entropia/vaporlight/vaporware/led-boards/stm_include/stm32/spi.h

/*
 * This file is part of the libopencm3 project.
 *
 * Copyright (C) 2009 Uwe Hermann <uwe@hermann-uwe.de>
 *
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
 * You should have received a copy of the GNU Lesser General Public License
 * along with this program.  If not, see <http://www.gnu.org/licenses/>.
 */

#ifndef LIBOPENCM3_SPI_H
#define LIBOPENCM3_SPI_H

#include "memorymap.h"
#include "../cm3/common.h"

/* Registers can be accessed as 16bit or 32bit values. */

/* --- Convenience macros -------------------------------------------------- */

#define SPI1				SPI1_BASE
#define SPI2				SPI2_I2S_BASE
#define SPI3				SPI3_I2S_BASE

/* --- SPI registers ------------------------------------------------------- */

/* Control register 1 (SPIx_CR1) */
#define SPI_CR1(spi_base)		MMIO32(spi_base + 0x00)
#define SPI1_CR1			SPI_CR1(SPI1_BASE)
#define SPI2_CR1			SPI_CR1(SPI2_I2S_BASE)
#define SPI3_CR1			SPI_CR1(SPI3_I2S_BASE)

/* Control register 2 (SPIx_CR2) */
#define SPI_CR2(spi_base)		MMIO32(spi_base + 0x04)
#define SPI1_CR2			SPI_CR2(SPI1_BASE)
#define SPI2_CR2			SPI_CR2(SPI2_I2S_BASE)
#define SPI3_CR2			SPI_CR2(SPI3_I2S_BASE)

/* Status register (SPIx_SR) */
#define SPI_SR(spi_base)		MMIO32(spi_base + 0x08)
#define SPI1_SR				SPI_SR(SPI1_BASE)
#define SPI2_SR				SPI_SR(SPI2_I2S_BASE)
#define SPI3_SR				SPI_SR(SPI3_I2S_BASE)

/* Data register (SPIx_DR) */
#define SPI_DR(spi_base)		MMIO32(spi_base + 0x0c)
#define SPI1_DR				SPI_DR(SPI1_BASE)
#define SPI2_DR				SPI_DR(SPI2_I2S_BASE)
#define SPI3_DR				SPI_DR(SPI3_I2S_BASE)

/* CRC polynomial register (SPIx_CRCPR) */
/* Note: Not used in I2S mode. */
#define SPI_CRCPR(spi_base)		MMIO32(spi_base + 0x10)
#define SPI1_CRCPR			SPI_CRCPR(SPI1_BASE)
#define SPI2_CRCPR			SPI_CRCPR(SPI2_I2S_BASE)
#define SPI3_CRCPR			SPI_CRCPR(SPI3_I2S_BASE)

/* RX CRC register (SPIx_RXCRCR) */
/* Note: Not used in I2S mode. */
#define SPI_RXCRCR(spi_base)		MMIO32(spi_base + 0x14)
#define SPI1_RXCRCR			SPI_RXCRCR(SPI1_BASE)
#define SPI2_RXCRCR			SPI_RXCRCR(SPI2_I2S_BASE)
#define SPI3_RXCRCR			SPI_RXCRCR(SPI3_I2S_BASE)

/* TX CRC register (SPIx_RXCRCR) */
/* Note: Not used in I2S mode. */
#define SPI_TXCRCR(spi_base)		MMIO32(spi_base + 0x18)
#define SPI1_TXCRCR			SPI_TXCRCR(SPI1_BASE)
#define SPI2_TXCRCR			SPI_TXCRCR(SPI2_I2S_BASE)
#define SPI3_TXCRCR			SPI_TXCRCR(SPI3_I2S_BASE)

/* I2S configuration register (SPIx_I2SCFGR) */
#define SPI_I2SCFGR(spi_base)		MMIO32(spi_base + 0x1c)
#define SPI1_I2SCFGR			SPI_I2SCFGR(SPI1_BASE)
#define SPI2_I2SCFGR			SPI_I2SCFGR(SPI2_I2S_BASE)
#define SPI3_I2SCFGR			SPI_I2SCFGR(SPI3_I2S_BASE)

/* I2S prescaler register (SPIx_I2SPR) */
#define SPI_I2SPR(spi_base)		MMIO32(spi_base + 0x20)
#define SPI1_I2SPR			SPI_I2SPR(SPI1_BASE)
#define SPI2_I2SPR			SPI_I2SPR(SPI2_I2S_BASE)
#define SPI3_I2SPR			SPI_I2SPR(SPI3_I2S_BASE)

/* --- SPI_CR1 values ------------------------------------------------------ */

/* Note: None of the CR1 bits are used in I2S mode. */

/* BIDIMODE: Bidirectional data mode enable */
#define SPI_CR1_BIDIMODE_2LINE_UNIDIR	(0 << 15)
#define SPI_CR1_BIDIMODE_1LINE_BIDIR	(1 << 15)
#define SPI_CR1_BIDIMODE		(1 << 15)

/* BIDIOE: Output enable in bidirectional mode */
#define SPI_CR1_BIDIOE			(1 << 14)

/* CRCEN: Hardware CRC calculation enable */
#define SPI_CR1_CRCEN			(1 << 13)

/* CRCNEXT: Transmit CRC next */
#define SPI_CR1_CRCNEXT			(1 << 12)

/* DFF: Data frame format */
#define SPI_CR1_DFF_8BIT		(0 << 11)
#define SPI_CR1_DFF_16BIT		(1 << 11)
#define SPI_CR1_DFF			(1 << 11)

/* RXONLY: Receive only */
#define SPI_CR1_RXONLY			(1 << 10)

/* SSM: Software slave management */
#define SPI_CR1_SSM			(1 << 9)

/* SSI: Internal slave select */
#define SPI_CR1_SSI			(1 << 8)

/* LSBFIRST: Frame format */
#define SPI_CR1_MSBFIRST		(0 << 7)
#define SPI_CR1_LSBFIRST		(1 << 7)

/* SPE: SPI enable */
#define SPI_CR1_SPE			(1 << 6)

/* BR[2:0]: Baud rate control */
#define SPI_CR1_BAUDRATE_FPCLK_DIV_2	(0x00 << 3)
#define SPI_CR1_BAUDRATE_FPCLK_DIV_4	(0x01 << 3)
#define SPI_CR1_BAUDRATE_FPCLK_DIV_8	(0x02 << 3)
#define SPI_CR1_BAUDRATE_FPCLK_DIV_16	(0x03 << 3)
#define SPI_CR1_BAUDRATE_FPCLK_DIV_32	(0x04 << 3)
#define SPI_CR1_BAUDRATE_FPCLK_DIV_64	(0x05 << 3)
#define SPI_CR1_BAUDRATE_FPCLK_DIV_128	(0x06 << 3)
#define SPI_CR1_BAUDRATE_FPCLK_DIV_256	(0x07 << 3)
#define SPI_CR1_BR_FPCLK_DIV_2		0x0
#define SPI_CR1_BR_FPCLK_DIV_4		0x1
#define SPI_CR1_BR_FPCLK_DIV_8		0x2
#define SPI_CR1_BR_FPCLK_DIV_16		0x3
#define SPI_CR1_BR_FPCLK_DIV_32		0x4
#define SPI_CR1_BR_FPCLK_DIV_64		0x5
#define SPI_CR1_BR_FPCLK_DIV_128	0x6
#define SPI_CR1_BR_FPCLK_DIV_256	0x7

/* MSTR: Master selection */
#define SPI_CR1_MSTR			(1 << 2)

/* CPOL: Clock polarity */
#define SPI_CR1_CPOL_CLK_TO_0_WHEN_IDLE	(0 << 1)
#define SPI_CR1_CPOL_CLK_TO_1_WHEN_IDLE	(1 << 1)
#define SPI_CR1_CPOL			(1 << 1)

/* CPHA: Clock phase */
#define SPI_CR1_CPHA_CLK_TRANSITION_1	(0 << 0)
#define SPI_CR1_CPHA_CLK_TRANSITION_2	(1 << 0)
#define SPI_CR1_CPHA			(1 << 0)

/* --- SPI_CR1 values ------------------------------------------------------ */

/* Bits [15:8]: Reserved. Forced to 0 by hardware. */

/* TXEIE: Tx buffer empty interrupt enable */
#define SPI_CR2_TXEIE			(1 << 7)

/* RXNEIE: RX buffer not empty interrupt enable */
#define SPI_CR2_RXNEIE			(1 << 6)

/* ERRIE: Error interrupt enable */
#define SPI_CR2_ERRIE			(1 << 5)

/* Bits [4:3]: Reserved. Forced to 0 by hardware. */

/* SSOE: SS output enable */
#define SPI_CR2_SSOE			(1 << 2)

/* TXDMAEN: Tx buffer DMA enable */
#define SPI_CR2_TXDMAEN			(1 << 1)

/* RXDMAEN: Rx buffer DMA enable */
#define SPI_CR2_RXDMAEN			(1 << 0)

/* --- SPI_SR values ------------------------------------------------------- */

/* Bits [15:8]: Reserved. Forced to 0 by hardware. */

/* BSY: Busy flag */
#define SPI_SR_BSY			(1 << 7)

/* OVR: Overrun flag */
#define SPI_SR_OVR			(1 << 6)

/* MODF: Mode fault */
#define SPI_SR_MODF			(1 << 5)

/* CRCERR: CRC error flag */
#define SPI_SR_CRCERR			(1 << 4)

/* UDR: Underrun flag */
#define SPI_SR_UDR			(1 << 3)

/* CHSIDE: Channel side */
#define SPI_SR_CHSIDE			(1 << 2)

/* TXE: Transmit buffer empty */
#define SPI_SR_TXE			(1 << 1)

/* RXNE: Receive buffer not empty */
#define SPI_SR_RXNE			(1 << 0)

/* --- SPI_SR values ------------------------------------------------------- */

/* SPI_DR[15:0]: Data Register. */

/* --- SPI_CRCPR values ---------------------------------------------------- */

/* SPI_CRCPR [15:0]: CRC Polynomial Register. */

/* --- SPI_RXCRCR values --------------------------------------------------- */

/* SPI_RXCRCR [15:0]: RX CRC Register. */

/* --- SPI_TXCRCR values --------------------------------------------------- */

/* SPI_TXCRCR [15:0]: TX CRC Register. */

/* --- SPI_I2SCFGR values -------------------------------------------------- */

/* Bits [15:12]: Reserved. Forced to 0 by hardware. */

/* I2SMOD: I2S mode selection */
#define SPI_I2SCFGR_I2SMOD			(1 << 11)

/* I2SE: I2S Enable */
#define SPI_I2SCFGR_I2SE			(1 << 10)

/* I2SCFG[9:8]: I2S configuration mode */
#define SPI_I2SCFGR_I2SCFG_LSB			8
#define SPI_I2SCFGR_I2SCFG_SLAVE_TRANSMIT	0x0
#define SPI_I2SCFGR_I2SCFG_SLAVE_RECEIVE	0x1
#define SPI_I2SCFGR_I2SCFG_MASTER_TRANSMIT	0x2
#define SPI_I2SCFGR_I2SCFG_MASTER_RECEIVE	0x3

/* PCMSYNC: PCM frame synchronization */
#define SPI_I2SCFGR_PCMSYNC			(1 << 7)

/* Bit 6: Reserved. Forced to 0 by hardware. */

/* I2SSTD[5:4]: I2S standard selection */
#define SPI_I2SCFGR_I2SSTD_LSB			4
#define SPI_I2SCFGR_I2SSTD_I2S_PHILLIPS		0x0
#define SPI_I2SCFGR_I2SSTD_MSB_JUSTIFIED	0x1
#define SPI_I2SCFGR_I2SSTD_LSB_JUSTIFIED	0x2
#define SPI_I2SCFGR_I2SSTD_PCM			0x3

/* CKPOL: Steady state clock polarity */
#define SPI_I2SCFGR_CKPOL			(1 << 3)

/* DATLEN[2:1]: Data length to be transferred */
#define SPI_I2SCFGR_DATLEN_LSB			1
#define SPI_I2SCFGR_DATLEN_16BIT		0x0
#define SPI_I2SCFGR_DATLEN_24BIT		0x1
#define SPI_I2SCFGR_DATLEN_32BIT		0x2

/* CHLEN: Channel length */
#define SPI_I2SCFGR_CHLEN			(1 << 0)

/* --- SPI_I2SPR values ---------------------------------------------------- */

/* Bits [15:10]: Reserved. Forced to 0 by hardware. */

/* MCKOE: Master clock output enable */
#define SPI_I2SPR_MCKOE				(1 << 9)

/* ODD: Odd factor for the prescaler */
#define SPI_I2SPR_ODD				(1 << 8)

/* I2SDIV[7:0]: I2S Linear prescaler */
/* 0 and 1 are forbidden values */

#endif
