entropia/vaporlight/vaporware/led-boards/stm_include/stm32/scb.h

/*
 * This file is part of the libopencm3 project.
 *
 * Copyright (C) 2010 Piotr Esden-Tempski <piotr@esden.net>
 * Copyright (C) 2010 Thomas Otto <tommi@viadmin.org>
 *
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
 * You should have received a copy of the GNU Lesser General Public License
 * along with this program.  If not, see <http://www.gnu.org/licenses/>.
 */

#ifndef LIBOPENCM3_SCB_H
#define LIBOPENCM3_SCB_H

#include "memorymap.h"
#include "../cm3/common.h"

/* --- SCB: Registers ------------------------------------------------------ */

/* CPUID: CPUID base register */
#define SCB_CPUID                       MMIO32(SCB_BASE + 0x00)

/* ICSR: Interrupt Control State Register */
#define SCB_ICSR                        MMIO32(SCB_BASE + 0x04)

/* VTOR: Vector Table Offset Register */
#define SCB_VTOR                        MMIO32(SCB_BASE + 0x08)

/* AIRCR: Application Interrupt and Reset Control Register */
#define SCB_AIRCR                       MMIO32(SCB_BASE + 0x0C)

/* SCR: System Control Register */
#define SCB_SCR                         MMIO32(SCB_BASE + 0x10)

/* CCR: Configuration Control Register */
#define SCB_CCR                         MMIO32(SCB_BASE + 0x14)

/* SHP: System Handler Priority Registers */
/* Note: 12 8bit registers */
#define SCB_SHPR(shpr_id)               MMIO8(SCB_BASE + 0x18 + shpr_id)
#define SCB_SHPR1			MMIO8(SCB_BASE + 0x18 + 1)
#define SCB_SHPR2			MMIO8(SCB_BASE + 0x18 + 2)
#define SCB_SHPR3			MMIO8(SCB_BASE + 0x18 + 3)

/* SHCSR: System Handler Control and State Register */
#define SCB_SHCSR                       MMIO32(SCB_BASE + 0x24)

/* CFSR: Configurable Fault Status Registers */
#define SCB_CFSR                        MMIO32(SCB_BASE + 0x28)

/* HFSR: Hard Fault Status Register */
#define SCB_HFSR                        MMIO32(SCB_BASE + 0x2C)

/* DFSR: Debug Fault Status Register */
#define SCB_DFSR                        MMIO32(SCB_BASE + 0x30)

/* MMFAR: Memory Manage Fault Address Register */
#define SCB_MMFAR                       MMIO32(SCB_BASE + 0x34)

/* BFAR: Bus Fault Address Register */
#define SCB_BFAR                        MMIO32(SCB_BASE + 0x38)

/* AFSR: Auxiliary Fault Status Register */
#define SCB_AFSR                        MMIO32(SCB_BASE + 0x3C)

/* --- SCB values ---------------------------------------------------------- */

/* --- SCB_CPUID values ---------------------------------------------------- */

/* Implementer[31:24]: Implementer code */
#define SCP_CPUID_IMPLEMENTER_LSB		24
/* Variant[23:20]: Variant number */
#define SCP_CPUID_VARIANT_LSB			20
/* Constant[19:16]: Reads as 0xF */
#define SCP_CPUID_CONSTANT_LSB			16
/* PartNo[15:4]: Part number of the processor */
#define SCP_CPUID_PARTNO_LSB			4
/* Revision[3:0]: Revision number */
#define SCP_CPUID_REVISION_LSB			0

/* --- SCB_ICSR values ----------------------------------------------------- */

/* NMIPENDSET: NMI set-pending bit */
#define SCB_ICSR_NMIPENDSET			(1 << 31)
/* Bits [30:29]: reserved - must be kept cleared */
/* PENDSVSET: PendSV set-pending bit */
#define SCB_ICSR_PENDSVSET			(1 << 28)
/* PENDSVCLR: PendSV clear-pending bit */
#define SCB_ICSR_PENDSVCLR			(1 << 27)
/* PENDSTSET: SysTick exception set-pending bit */
#define SCB_ICSR_PENDSTSET			(1 << 26)
/* PENDSTCLR: SysTick exception clear-pending bit */
#define SCB_ICSR_PENDSTCLR			(1 << 25)
/* Bit 24: reserved - must be kept cleared */
/* Bit 23: reserved for debug - reads as 0 when not in debug mode */
/* ISRPENDING: Interrupt pending flag, excluding NMI and Faults */
#define SCB_ICSR_ISRPENDING			(1 << 22)
/* VECTPENDING[21:12] Pending vector */
#define SCB_ICSR_VECTPENDING_LSB		12
/* RETOBASE: Return to base level */
#define SCB_ICSR_RETOBASE			(1 << 11)
/* Bits [10:9]: reserved - must be kept cleared */
/* VECTACTIVE[8:0] Active vector */
#define SCB_ICSR_VECTACTIVE_LSB			0

/* --- SCB_VTOR values ----------------------------------------------------- */

/* Bits [31:30]: reserved - must be kept cleared */
/* TBLOFF[29:9]: Vector table base offset field */
#define SCB_VTOR_TBLOFF_LSB			9	/* inconsistent datasheet - LSB could be 11 */

/* --- SCB_AIRCR values ---------------------------------------------------- */

/* VECTKEYSTAT[31:16]/ VECTKEY[31:16] Register key */
#define SCB_AIRCR_VECTKEYSTAT_LSB		16
#define SCB_AIRCR_VECTKEY			0x05FA0000
/* ENDIANESS Data endianness bit */
#define SCB_AIRCR_ENDIANESS			(1 << 15)
/* Bits [14:11]: reserved - must be kept cleared */
/* PRIGROUP[10:8]: Interrupt priority grouping field */
#define SCB_AIRCR_PRIGROUP_LSB			8
#define SCB_AIRCR_PRIGROUP_GROUP16_NOSUB	0x3
#define SCB_AIRCR_PRIGROUP_GROUP8_SUB2		0x4
#define SCB_AIRCR_PRIGROUP_GROUP4_SUB4		0x5
#define SCB_AIRCR_PRIGROUP_GROUP2_SUB8		0x6
#define SCB_AIRCR_PRIGROUP_NOGROUP_SUB16	0x7
/* Bits [7:3]: reserved - must be kept cleared */
/* SYSRESETREQ System reset request */
#define SCB_AIRCR_SYSRESETREQ			(1 << 2)
/* VECTCLRACTIVE */
#define SCB_AIRCR_VECTCLRACTIVE			(1 << 1)
/* VECTRESET */
#define SCB_AIRCR_VECTRESET			(1 << 0)

/* --- SCB_SCR values ------------------------------------------------------ */

/* Bits [31:5]: reserved - must be kept cleared */
/* SEVEONPEND Send Event on Pending bit */
#define SCB_SCR_SEVEONPEND			(1 << 4)
/* Bit 3: reserved - must be kept cleared */
/* SLEEPDEEP */
#define SCB_SCR_SLEEPDEEP			(1 << 2)
/* SLEEPONEXIT */
#define SCB_SCR_SLEEPONEXIT			(1 << 1)
/* Bit 0: reserved - must be kept cleared */

/* --- SCB_CCR values ------------------------------------------------------ */

/* Bits [31:10]: reserved - must be kept cleared */
/* STKALIGN */
#define SCB_CCR_STKALIGN			(1 << 9)
/* BFHFNMIGN */
#define SCB_CCR_BFHFNMIGN			(1 << 8)
/* Bits [7:5]: reserved - must be kept cleared */
/* DIV_0_TRP */
#define SCB_CCR_DIV_0_TRP			(1 << 4)
/* UNALIGN_TRP */
#define SCB_CCR_UNALIGN_TRP			(1 << 3)
/* Bit 2: reserved - must be kept cleared */
/* USERSETMPEND */
#define SCB_CCR_USERSETMPEND			(1 << 1)
/* NONBASETHRDENA */
#define SCB_CCR_NONBASETHRDENA			(1 << 0)

/* --- SCB_SHPR1 values ---------------------------------------------------- */

/* Bits [31:24]: reserved - must be kept cleared */
/* PRI_6[23:16]: Priority of system handler 6, usage fault */
#define SCB_SHPR1_PRI_6_LSB			16
/* PRI_5[15:8]: Priority of system handler 5, bus fault */
#define SCB_SHPR1_PRI_5_LSB			8
/* PRI_4[7:0]: Priority of system handler 4, memory management fault */
#define SCB_SHPR1_PRI_4_LSB			0

/* --- SCB_SHPR2 values ---------------------------------------------------- */

/* PRI_11[31:24]: Priority of system handler 11, SVCall */
#define SCB_SHPR2_PRI_11_LSB			24
/* Bits [23:0]: reserved - must be kept cleared */

/* --- SCB_SHPR3 values ---------------------------------------------------- */

/* PRI_15[31:24]: Priority of system handler 15, SysTick exception */
#define SCB_SHPR3_PRI_15_LSB			24
/* PRI_14[23:16]: Priority of system handler 14, PendSV */
#define SCB_SHPR3_PRI_14_LSB			16
/* Bits [15:0]: reserved - must be kept cleared */

/* --- SCB_SHCSR values ---------------------------------------------------- */

/* Bits [31:19]: reserved - must be kept cleared */
/* USGFAULTENA: Usage fault enable */
#define SCB_SHCSR_USGFAULTENA			(1 << 18)
/* BUSFAULTENA: Bus fault enable */
#define SCB_SHCSR_BUSFAULTENA			(1 << 17)
/* MEMFAULTENA: Memory management fault enable */
#define SCB_SHCSR_MEMFAULTENA			(1 << 16)
/* SVCALLPENDED: SVC call pending */
#define SCB_SHCSR_SVCALLPENDED			(1 << 15)
/* BUSFAULTPENDED: Bus fault exception pending */
#define SCB_SHCSR_BUSFAULTPENDED		(1 << 14)
/* MEMFAULTPENDED: Memory management fault exception pending */
#define SCB_SHCSR_MEMFAULTPENDED		(1 << 13)
/* USGFAULTPENDED: Usage fault exception pending */
#define SCB_SHCSR_USGFAULTPENDED		(1 << 12)
/* SYSTICKACT: SysTick exception active */
#define SCB_SHCSR_SYSTICKACT			(1 << 11)
/* PENDSVACT: PendSV exception active */
#define SCB_SHCSR_PENDSVACT			(1 << 10)
/* Bit 9: reserved - must be kept cleared */
/* MONITORACT: Debug monitor active */
#define SCB_SHCSR_MONITORACT			(1 << 8)
/* SVCALLACT: SVC call active */
#define SCB_SHCSR_SVCALLACT			(1 << 7)
/* Bits [6:4]: reserved - must be kept cleared */
/* USGFAULTACT: Usage fault exception active */
#define SCB_SHCSR_USGFAULTACT			(1 << 3)
/* Bit 2: reserved - must be kept cleared */
/* BUSFAULTACT: Bus fault exception active */
#define SCB_SHCSR_BUSFAULTACT			(1 << 1)
/* MEMFAULTACT: Memory management fault exception active */
#define SCB_SHCSR_MEMFAULTACT			(1 << 0)

/* --- SCB_CFSR values ----------------------------------------------------- */

/* Bits [31:26]: reserved - must be kept cleared */
/* DIVBYZERO: Divide by zero usage fault */
#define SCB_CFSR_DIVBYZERO			(1 << 25)
/* UNALIGNED: Unaligned access usage fault */
#define SCB_CFSR_UNALIGNED			(1 << 24)
/* Bits [23:20]: reserved - must be kept cleared */
/* NOCP: No coprocessor usage fault */
#define SCB_CFSR_NOCP				(1 << 19)
/* INVPC: Invalid PC load usage fault */
#define SCB_CFSR_INVPC				(1 << 18)
/* INVSTATE: Invalid state usage fault */
#define SCB_CFSR_INVSTATE			(1 << 17)
/* UNDEFINSTR: Undefined instruction usage fault */
#define SCB_CFSR_UNDEFINSTR			(1 << 16)
/* BFARVALID: Bus Fault Address Register (BFAR) valid flag */
#define SCB_CFSR_BFARVALID			(1 << 15)
/* Bits [14:13]: reserved - must be kept cleared */
/* STKERR: Bus fault on stacking for exception entry */
#define SCB_CFSR_STKERR				(1 << 12)
/* UNSTKERR: Bus fault on unstacking for a return from exception */
#define SCB_CFSR_UNSTKERR			(1 << 11)
/* IMPRECISERR: Imprecise data bus error */
#define SCB_CFSR_IMPRECISERR			(1 << 10)
/* PRECISERR: Precise data bus error */
#define SCB_CFSR_PRECISERR			(1 << 9)
/* IBUSERR: Instruction bus error */
#define SCB_CFSR_IBUSERR			(1 << 8)
/* MMARVALID: Memory Management Fault Address Register (MMAR) valid flag */
#define SCB_CFSR_MMARVALID			(1 << 7)
/* Bits [6:5]: reserved - must be kept cleared */
/* MSTKERR: Memory manager fault on stacking for exception entry */
#define SCB_CFSR_MSTKERR			(1 << 4)
/* MUNSTKERR: Memory manager fault on unstacking for a return from exception */
#define SCB_CFSR_MUNSTKERR			(1 << 3)
/* Bit 2: reserved - must be kept cleared */
/* DACCVIOL: Data access violation flag */
#define SCB_CFSR_DACCVIOL			(1 << 1)
/* IACCVIOL: Instruction access violation flag */
#define SCB_CFSR_IACCVIOL			(1 << 0)

/* --- SCB_HFSR values ----------------------------------------------------- */

/* DEBUG_VT: reserved for debug use */
#define SCB_HFSR_DEBUG_VT			(1 << 31)
/* FORCED: Forced hard fault */
#define SCB_HFSR_FORCED				(1 << 30)
/* Bits [29:2]: reserved - must be kept cleared */
/* VECTTBL: Vector table hard fault */
#define SCB_HFSR_VECTTBL			(1 << 1)
/* Bit 0: reserved - must be kept cleared */

/* --- SCB_MMFAR values ---------------------------------------------------- */

/* MMFAR [31:0]: Memory management fault address */

/* --- SCB_BFAR values ----------------------------------------------------- */

/* BFAR [31:0]: Bus fault address */

#endif
