entropia/vaporlight/pyVaporlight/config.py

lights = [
    [0, [12, 13, 14]],
    [0, [9, 10, 11]],
    [0, [6, 7, 8]],
    [0, [3, 4, 5]],
    [0, {0, 1, 2}],
    [1, {0, 1, 2}],
    [1, [3, 4, 5]],
    [1, [6, 7, 8]],
    [1, [9, 10, 11]],
    [1, [12, 13, 14]],
    [5, [0, 1, 2]],
    [5, [3, 4, 5]],
    [5, [6, 7, 8]],
    [5, [9, 10, 11]],
    [5, [12, 13, 14]],
    [3, [0, 1, 2]],
    [3, [3, 4, 5]],
    [3, [6, 7, 8]],
    [3, [9, 10, 11]],
    [3, [12, 13, 14]],
    [6, [0, 1, 2]],
    [6, [3, 4, 5]],
    [6, [6, 7, 8]],
    [6, [9, 10, 11]],
    [6, [12, 13, 14]],
    [2, [0, 1, 2]],
    [2, [3, 4, 5]],
    [2, [6, 7, 8]],
    [2, [9, 10, 11]],
    [2, [12, 13, 14]],
    [7, [0, 1, 2]],
    [7, [3, 4, 5]],
    [7, [6, 7, 8]],
    [7, [9, 10, 11]],
    [7, [12, 13, 14]]
]

port = {
    'device': "/dev/ttyUSB0",
    'baudrate': 500000
}
