entropia/vaporlight/vaporware/led-boards/stm_include/stm32/rtc.h

/*
 * This file is part of the libopencm3 project.
 *
 * Copyright (C) 2010 Uwe Hermann <uwe@hermann-uwe.de>
 *
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
 * You should have received a copy of the GNU Lesser General Public License
 * along with this program.  If not, see <http://www.gnu.org/licenses/>.
 */

#ifndef LIBOPENCM3_RTC_H
#define LIBOPENCM3_RTC_H

#include "memorymap.h"
#include "../cm3/common.h"
#include "pwr.h"

/* --- RTC registers ------------------------------------------------------- */

/* RTC control register high (RTC_CRH) */
#define RTC_CRH				MMIO32(RTC_BASE + 0x00)

/* RTC control register low (RTC_CRL) */
#define RTC_CRL				MMIO32(RTC_BASE + 0x04)

/* RTC prescaler load register (RTC_PRLH / RTC_PRLL) */
#define RTC_PRLH			MMIO32(RTC_BASE + 0x08)
#define RTC_PRLL			MMIO32(RTC_BASE + 0x0c)

/* RTC prescaler divider register (RTC_DIVH / RTC_DIVL) */
#define RTC_DIVH			MMIO32(RTC_BASE + 0x10)
#define RTC_DIVL			MMIO32(RTC_BASE + 0x14)

/* RTC counter register (RTC_CNTH / RTC_CNTL) */
#define RTC_CNTH			MMIO32(RTC_BASE + 0x18)
#define RTC_CNTL			MMIO32(RTC_BASE + 0x1c)

/* RTC alarm register high (RTC_ALRH / RTC_ALRL) */
#define RTC_ALRH			MMIO32(RTC_BASE + 0x20)
#define RTC_ALRL			MMIO32(RTC_BASE + 0x24)

/* --- RTC_CRH values -------------------------------------------------------*/

/* Note: Bits [15:3] are reserved, and forced to 0 by hardware. */

/* OWIE: Overflow interrupt enable */
#define RTC_CRH_OWIE			(1 << 2)

/* ALRIE: Alarm interrupt enable */
#define RTC_CRH_ALRIE			(1 << 1)

/* SECIE: Second interrupt enable */
#define RTC_CRH_SECIE			(1 << 0)

/* --- RTC_CRL values -------------------------------------------------------*/

/* Note: Bits [15:6] are reserved, and forced to 0 by hardware. */

/* RTOFF: RTC operation OFF */
#define RTC_CRL_RTOFF			(1 << 5)

/* CNF: Configuration flag */
#define RTC_CRL_CNF			(1 << 4)

/* RSF: Registers synchronized flag */
#define RTC_CRL_RSF			(1 << 3)

/* OWF: Overflow flag */
#define RTC_CRL_OWF			(1 << 2)

/* ALRF: Alarm flag */
#define RTC_CRL_ALRF			(1 << 1)

/* SECF: Second flag */
#define RTC_CRL_SECF			(1 << 0)

/* --- RTC_PRLH values ------------------------------------------------------*/

/* Note: Bits [15:4] are reserved, and forced to 0 by hardware. */

/* TODO */

/* --- RTC_PRLL values ------------------------------------------------------*/

/* TODO */

/* --- RTC_DIVH values ------------------------------------------------------*/

/* Bits [15:4] are reserved. */

/* TODO */

/* --- RTC_DIVL values ------------------------------------------------------*/

/* TODO */

/* --- RTC_CNTH values ------------------------------------------------------*/

/* TODO */

/* --- RTC_CNTL values ------------------------------------------------------*/

/* TODO */

/* --- RTC_ALRH values ------------------------------------------------------*/

/* TODO */

/* --- RTC_ALRL values ------------------------------------------------------*/

/* TODO */

#endif
