entropia/vaporlight/vaporware/led-boards/debug.h

/*
 * This module access to the debug USART and a few other debug-related
 * functions.
 */

#include "error.h"
#include "fixedpoint.h"

/*
 * Sends a character via the "debug TX" USART.
 */
void debug_putchar(const char message);

/*
 * Sends a message via the "debug TX" USART.
 */
void debug_write(const char *message, int length);

#define debug_string(str) debug_write(STR_WITH_LEN(str))

/*
 * Converts the last "width" nybbles of x to hexadecimal format and
 * sends them via the debug USART.
 */
void debug_hex(int x, int width);

/*
 * Converts the given integer to decimal format and sends it via the
 * debug USART. If the resulting string is shorter than min_width, it
 * is padded at the left with spaces.
 */
void debug_uint(unsigned int x, int min_width);
void debug_sint(unsigned int x, int min_width);

void debug_fixed(fixed_t x);

/*
 * Starts the cycle counter.
 */
void cycle_start();

/*
 * Returns the number of cycles elapsed since the cycle counter was
 * started.
 */
int cycle_get();

/*
 * Stops the cycle counter and returns the number of cycles elapsed
 * since it was started.
 */
int cycle_stop();
